perryPyn/Projet1A/docs/output/BottomCase.png

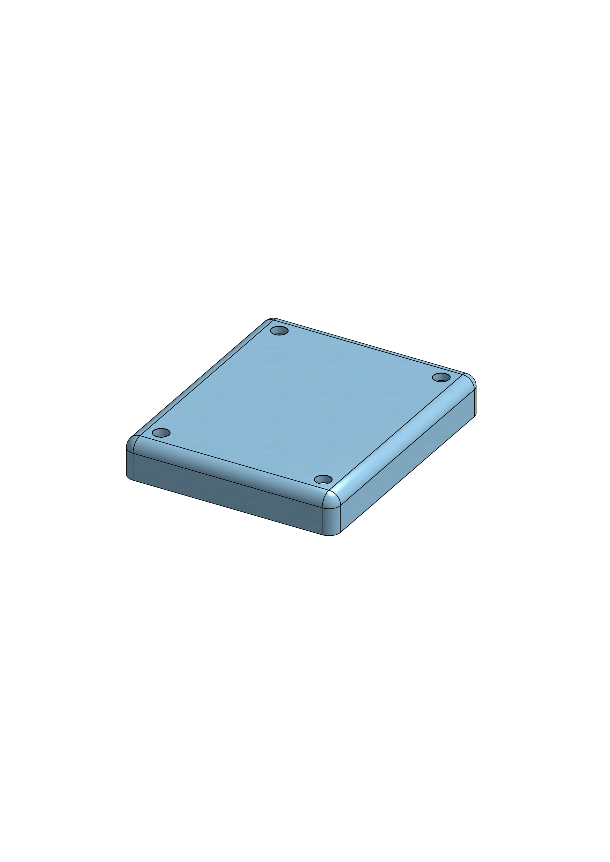
docs/output/BottomCase.png
