perryPyn/Projet1A/src/ATTinyDriver/display.c

#include "display.h"


void NumberToDisplay(uint8_t numberToDisplay) {
  /*
    *  numberToDiplsay est un entier entre 0 et 9
    *  Le décodeur est relié aux 4 pins dont l'état est géré par les bits 0 à 3 de PORTA
  */

  PORTA = (PORTA & 0xF0) | (numberToDisplay & 0x0F);
}

void DecimalToDisplay(void){
  PORTA |= (1 << PA5);
}

void DisplayToUse(uint8_t display) {
  PORTB = (PORTB & 0xF8) | (1 << display);
}

void DisplayOff(void) {
  /*
    *  Permet d'éteindre tout les afficheur et le point décimal
  */
  PORTB &= 0xF8;
}

void DecimalOff(void){
  PORTA &= ~(1 << PA5);
}
