perryPyn/Projet1A/src/ATTinyDriver/utils.h

#ifndef UTILS_H
#define UTILS_H

// #include <avr/io.h>
#include "gpio.h"
#include "display.h"


#ifdef __cplusplus
extern "C" {
#endif

void FormatNumber(uint16_t numberToSplit,volatile uint8_t* digit_unites,volatile uint8_t* digit_dizaines,volatile uint8_t* digit_centaines);
void DrawDecimalPoint(uint8_t display,uint8_t dp);
void DrawNumber(uint8_t display, uint8_t digit_1, uint8_t digit_2, uint8_t digit_3);

#ifdef __cplusplus
}
#endif

#endif
